Tonikiller10000/VIDEOCARD/VIDEOCARD_Pictures/General/20230708_223035.jpg

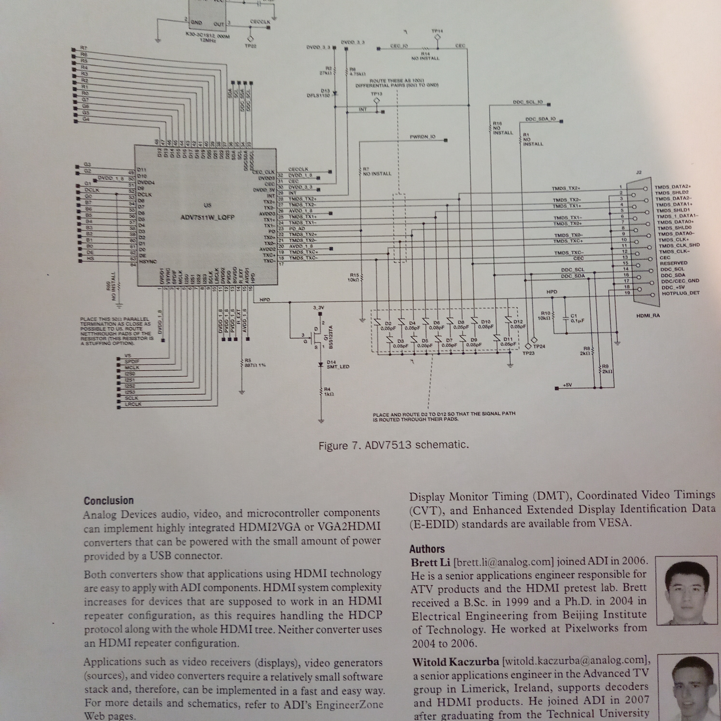
VIDEOCARD_Pictures/General/20230708_223035.jpg
