Tonikiller10000/VIDEOCARD/VIDEOCARD_Pictures/General/ana.png

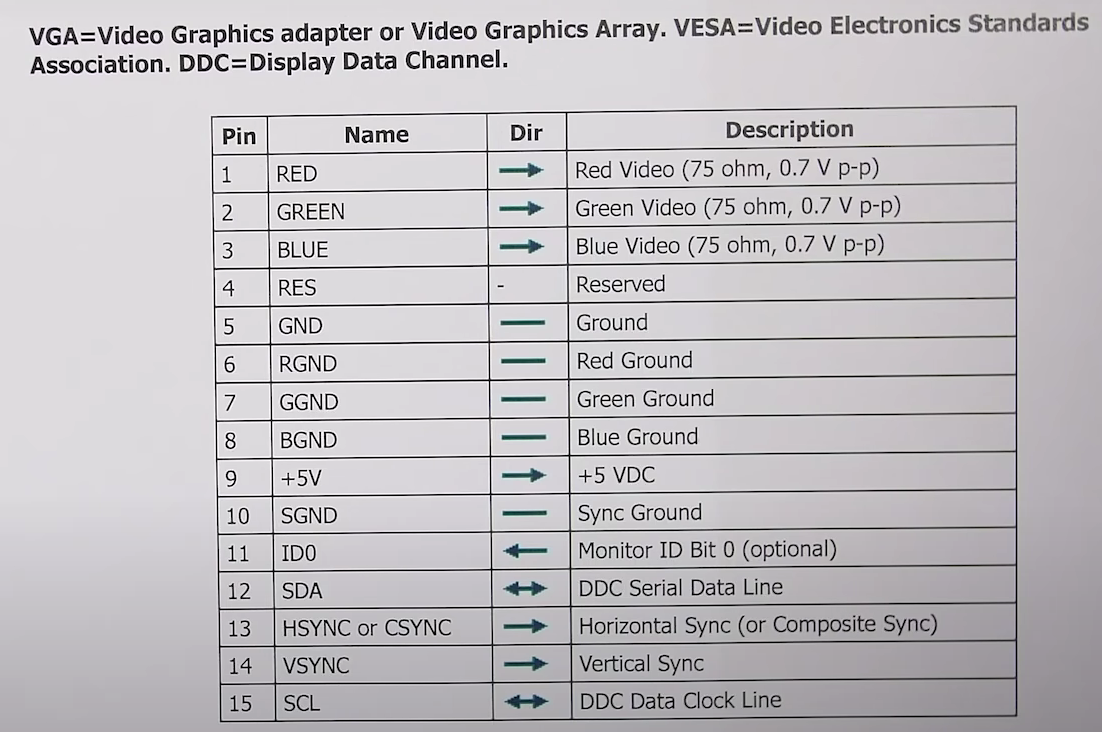
VIDEOCARD_Pictures/General/ana.png
