Tonikiller10000/VIDEOCARD/VIDEOCARD_Pictures/General/IMG-20220809-WA0004.jpeg

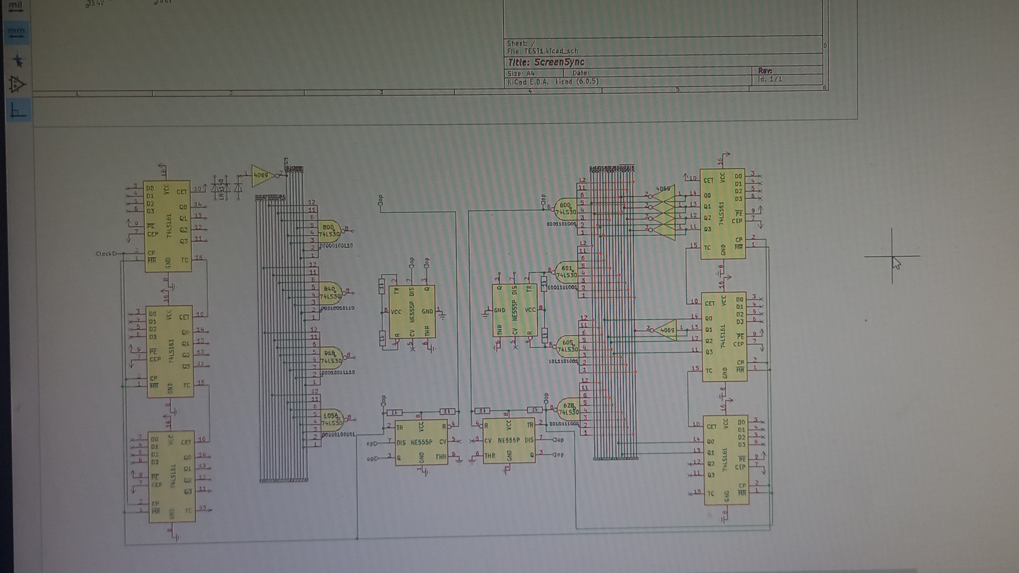
VIDEOCARD_Pictures/General/IMG-20220809-WA0004.jpeg
