Tonikiller10000/VIDEOCARD/VIDEOCARD_Pictures/General/IMG-20220909-WA0009.jpeg

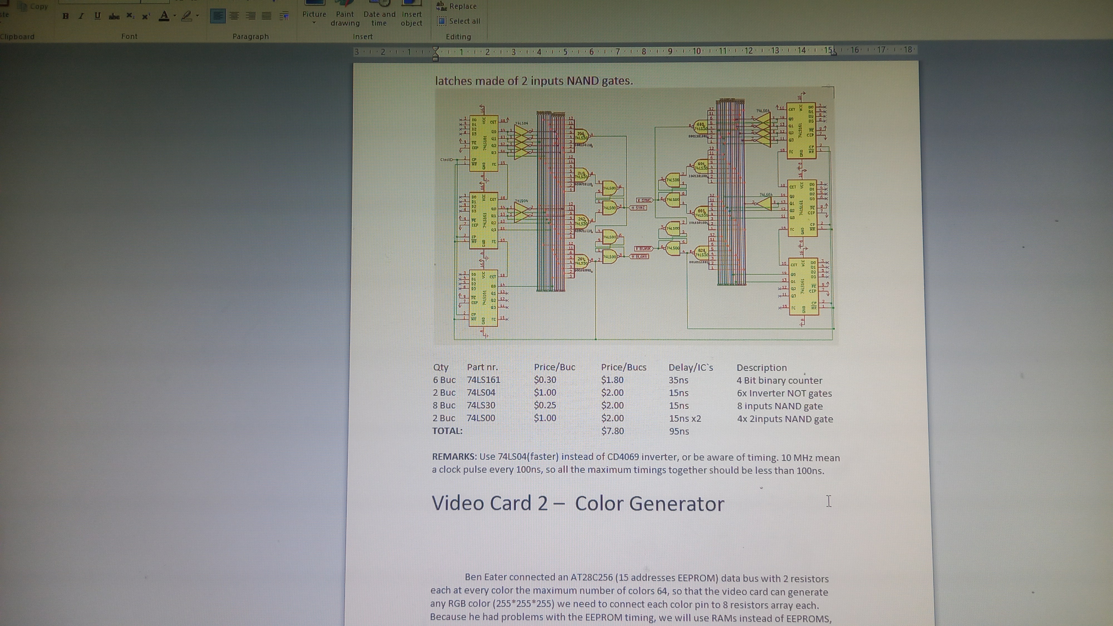
VIDEOCARD_Pictures/General/IMG-20220909-WA0009.jpeg
