Tonikiller10000/VIDEOCARD/VIDEOCARD_Pictures/General/res.png

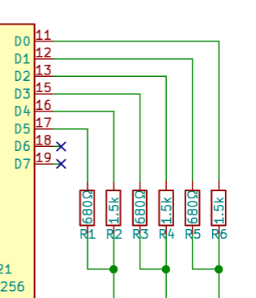
VIDEOCARD_Pictures/General/res.png
