Tonikiller10000/VIDEOCARD/VIDEOCARD_Pictures/General/rez2.png

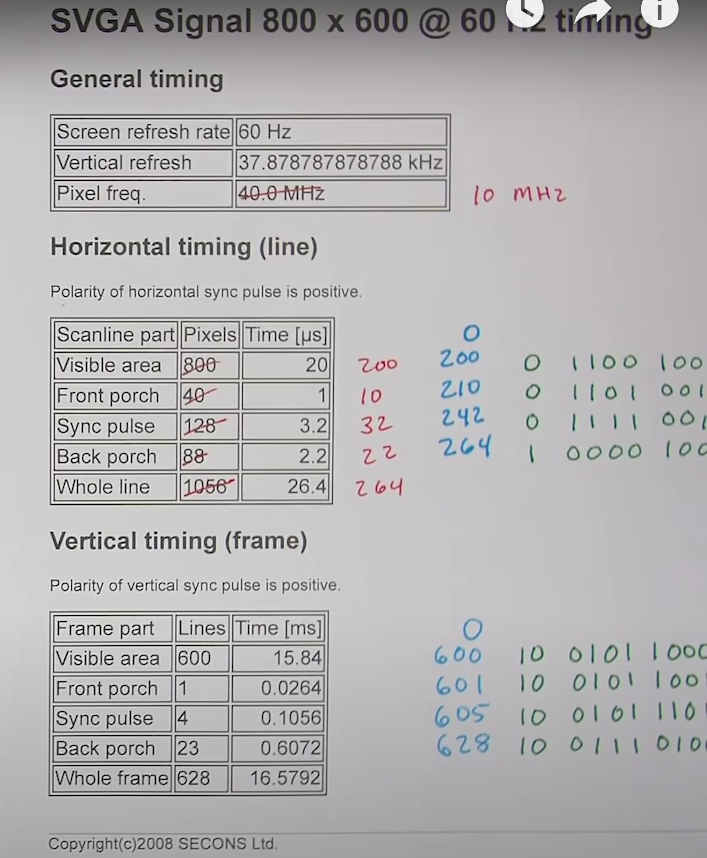
VIDEOCARD_Pictures/General/rez2.png
