Tonikiller10000/VIDEOCARD/VIDEOCARD_Pictures/General/rez.png

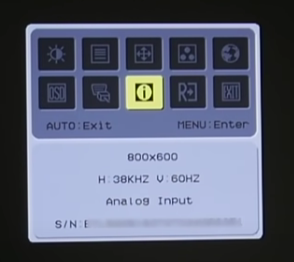
VIDEOCARD_Pictures/General/rez.png
