Tonikiller10000/VIDEOCARD/VIDEOCARD_Pictures/General/rezz.png

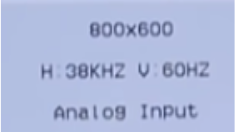
VIDEOCARD_Pictures/General/rezz.png
