Tonikiller10000/VIDEOCARD/VIDEOCARD_Pictures/General/rom.png

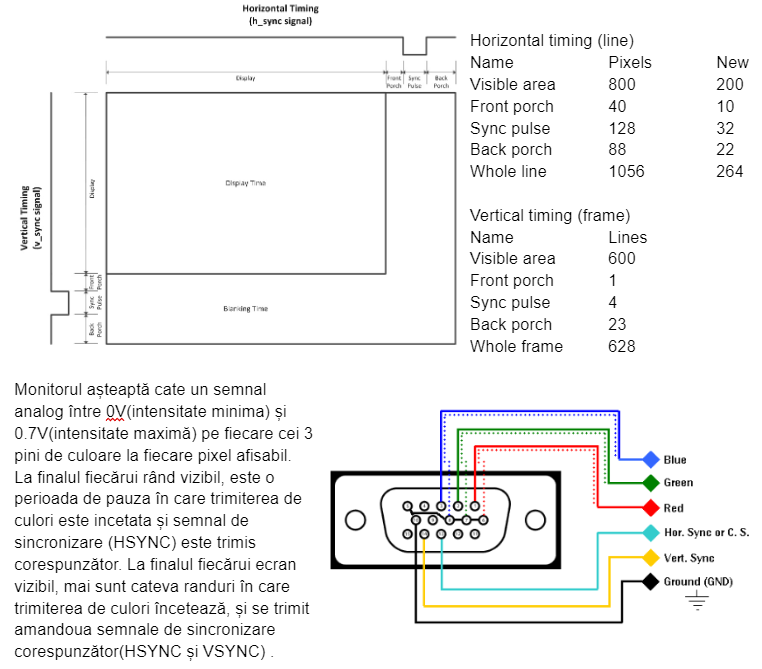
VIDEOCARD_Pictures/General/rom.png
