Tonikiller10000/VIDEOCARD/VIDEOCARD_Pictures/General/try.png

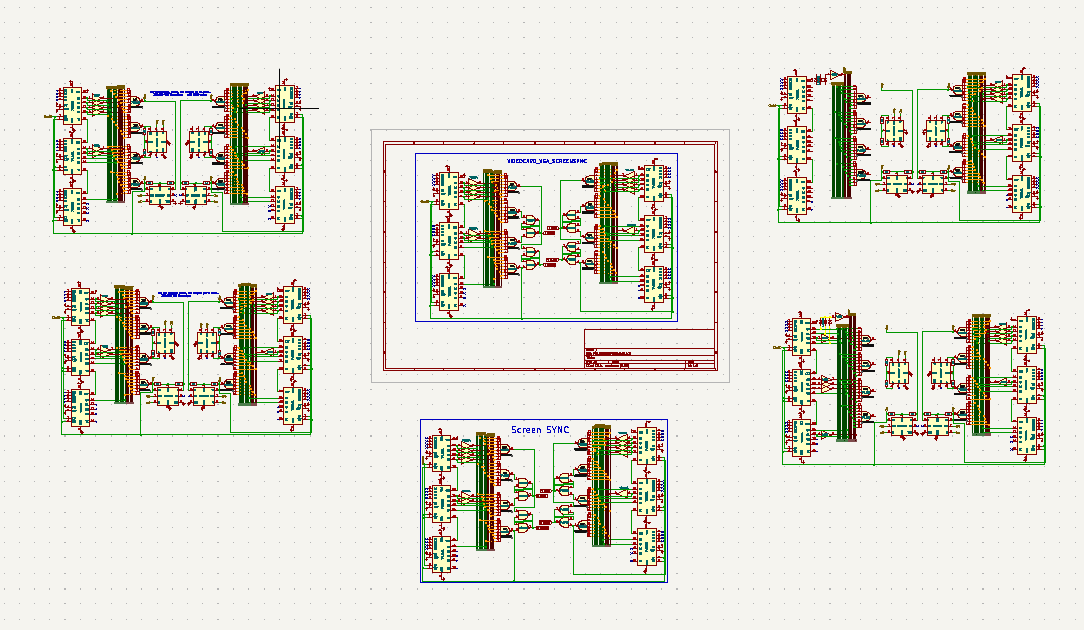
VIDEOCARD_Pictures/General/try.png
