Tonikiller10000/VIDEOCARD/VIDEOCARD_Pictures/General/vvv.png

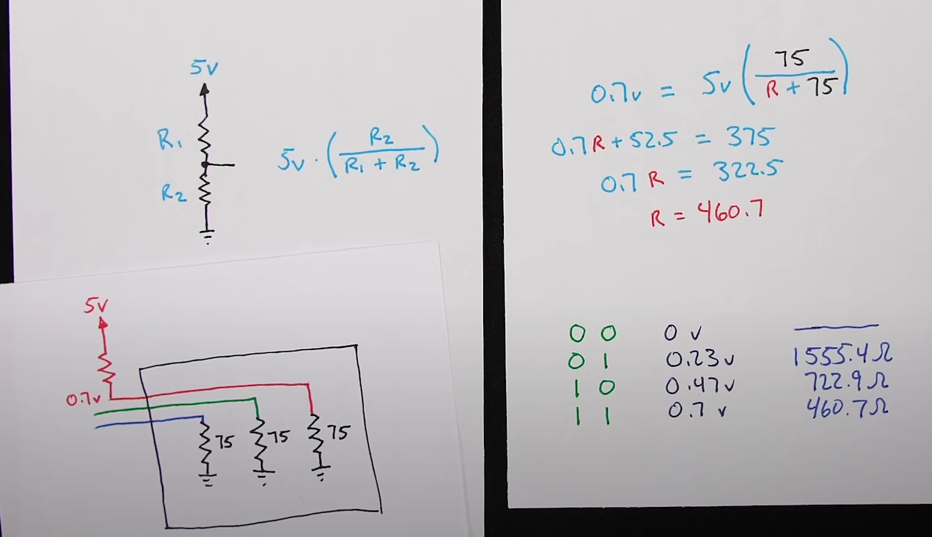
VIDEOCARD_Pictures/General/vvv.png
