Tonikiller10000/VIDEOCARD/VIDEOCARD_Pictures/General/{8A064546-B27A-44AC-BE49-6E5E956766A6}.png

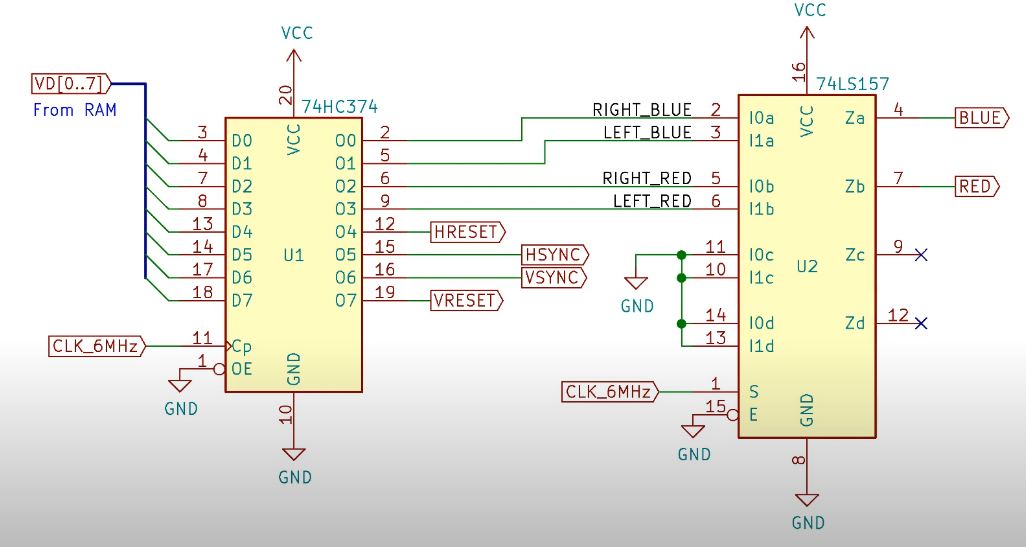
VIDEOCARD_Pictures/General/{8A064546-B27A-44AC-BE49-6E5E956766A6}.png
