Tonikiller10000/VIDEOCARD/VIDEOCARD_Pictures/General/{35AAB663-AD93-442C-8931-198A4515DB08}.png

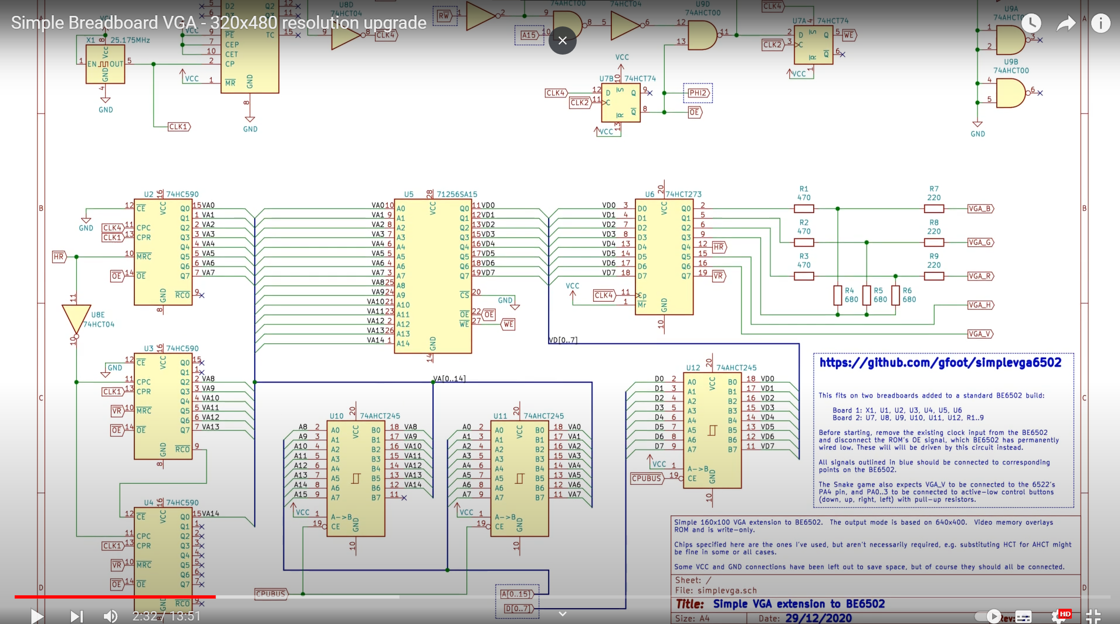
VIDEOCARD_Pictures/General/{35AAB663-AD93-442C-8931-198A4515DB08}.png
