Tonikiller10000/VIDEOCARD/VIDEOCARD_Pictures/V2.0/m1.png

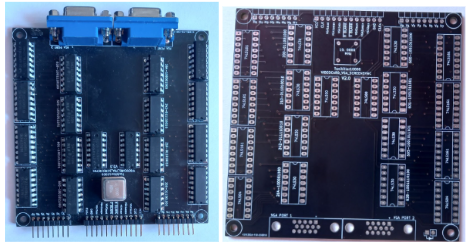
VIDEOCARD_Pictures/V2.0/m1.png
