Tonikiller10000/VIDEOCARD/VIDEOCARD_Pictures/V2.0/p1.png

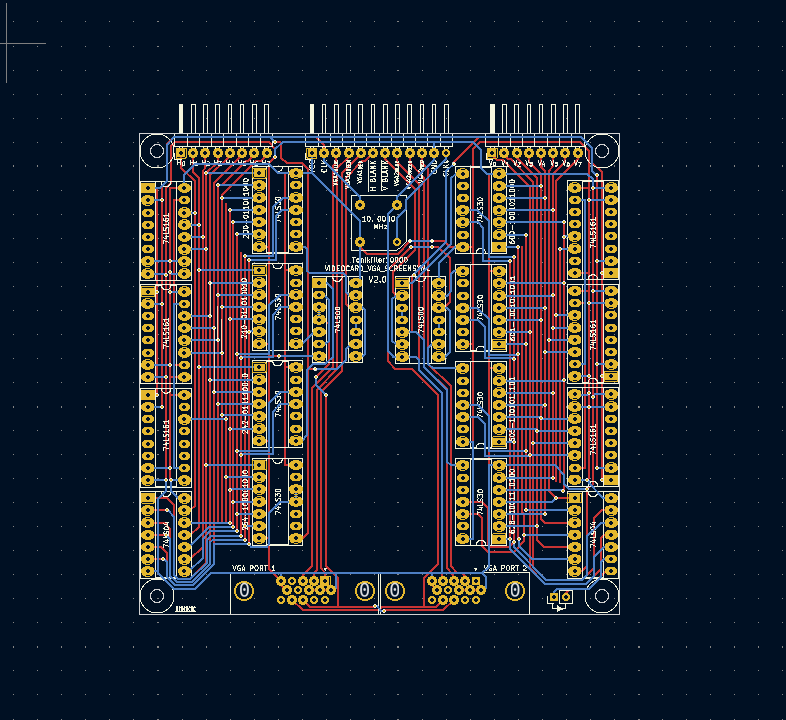
VIDEOCARD_Pictures/V2.0/p1.png
