Tonikiller10000/VIDEOCARD/VIDEOCARD_Pictures/V2.0/p4.jpeg

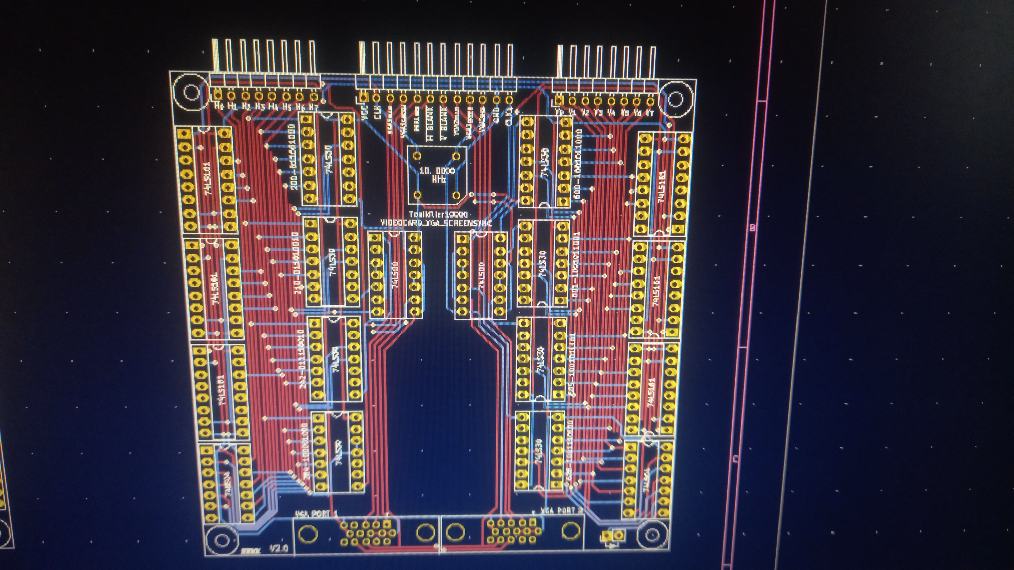
VIDEOCARD_Pictures/V2.0/p4.jpeg
