Tonikiller10000/VIDEOCARD/VIDEOCARD_Pictures/V2.0/r3.jpg

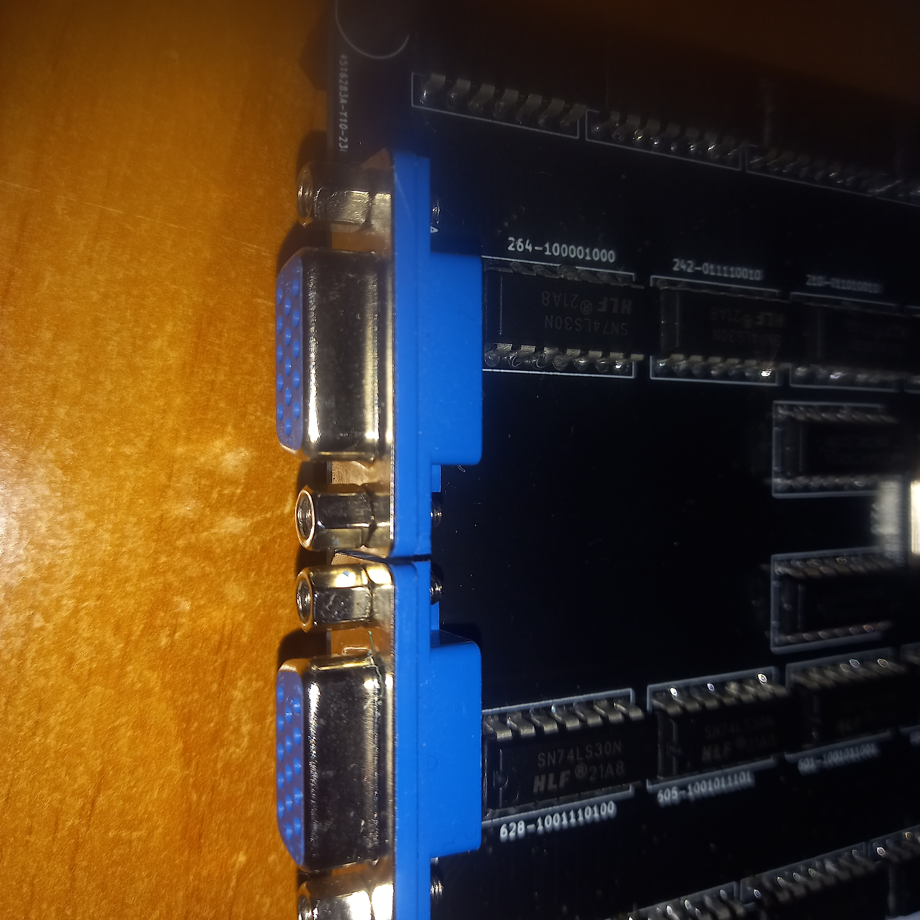
VIDEOCARD_Pictures/V2.0/r3.jpg
