Tonikiller10000/VIDEOCARD/VIDEOCARD_Pictures/V2.0/r5.jpg

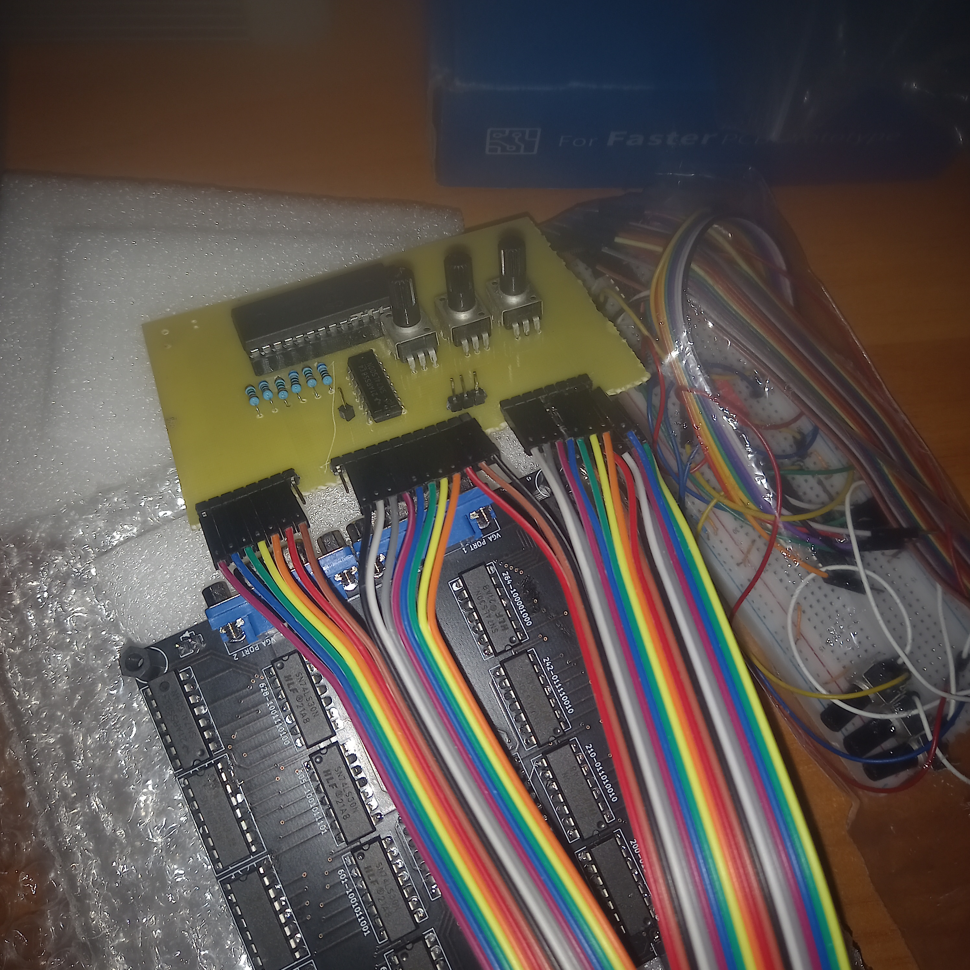
VIDEOCARD_Pictures/V2.0/r5.jpg
