Tonikiller10000/VIDEOCARD/VIDEOCARD_Pictures/V2.0/r6.jpg

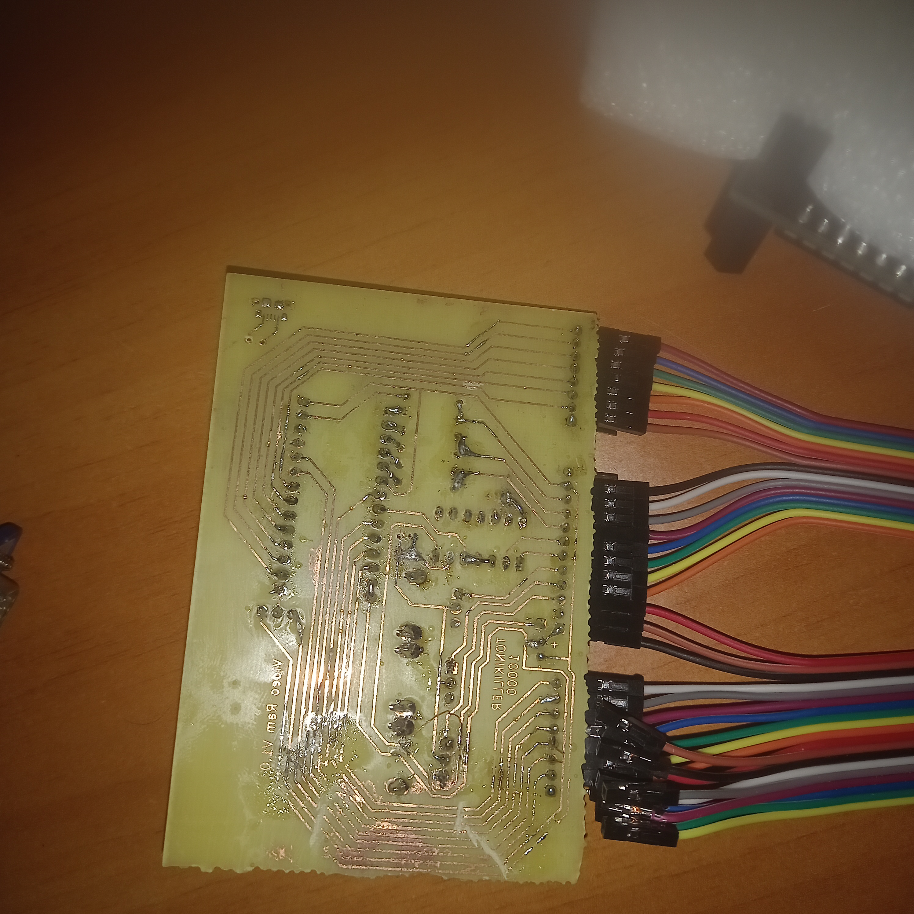
VIDEOCARD_Pictures/V2.0/r6.jpg
