Tonikiller10000/VIDEOCARD/VIDEOCARD_Pictures/V2.0/r8.png

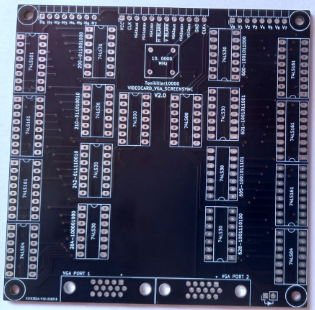
VIDEOCARD_Pictures/V2.0/r8.png
