Tonikiller10000/VIDEOCARD/VIDEOCARD_Pictures/General/IMG-20221229-WA0000.jpeg

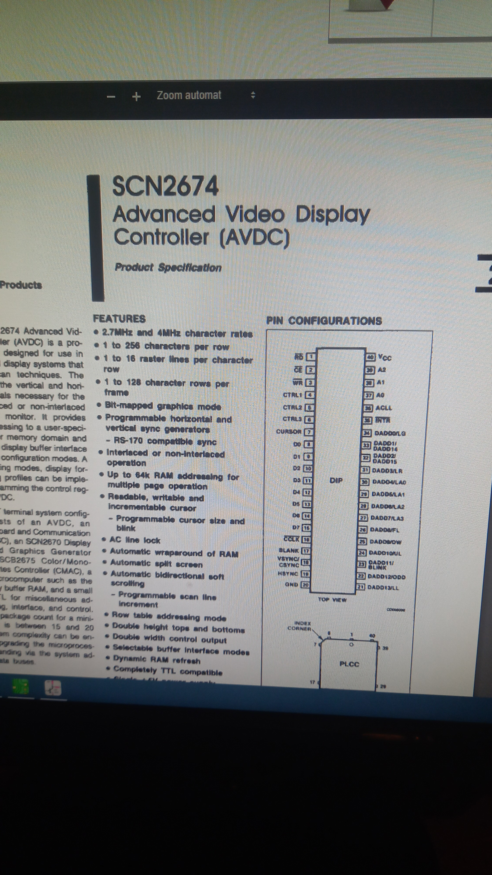
VIDEOCARD_Pictures/General/IMG-20221229-WA0000.jpeg
